topiko/bBot/Arduino/serial_due_rpi.ino

/*
  Serial Event example

  When new serial data arrives, this sketch adds it to a String.
  When a newline is received, the loop prints the string and clears it.

  A good test for this is to try it with a GPS receiver that sends out
  NMEA 0183 sentences.

  NOTE: The serialEvent() feature is not available on the Leonardo, Micro, or
  other ATmega32U4 based boards.

  created 9 May 2011
  by Tom Igoe

  This example code is in the public domain.

  http://www.arduino.cc/en/Tutorial/SerialEvent
*/

int inInt = 0;
int command[3] = {0, 0, 0};
int countSer = 0;
boolean report = false;  // whether the string is complete

void setup() {
  // initialize serial:
  Serial3.begin(115200);
}

void loop() {
  // print the int when newInt
  if (countSer == 1) {
    inInt += 1;
    commnad[0] = inInt;
  }
  else if (countSer == 2) {
    inInt += 2;
    commnad[1] = inInt;
  }
  else if (countSer == 3) {
    inInt += 3;
    commnad[2] = inInt;
    counter = 0;
    Serial3.print(command[0]);
    Serial3.print(command[1]);
    Serial3.print(command[2]);
  }
}

/*
  SerialEvent occurs whenever a new data comes in the hardware serial RX. This
  routine is run between each time loop() runs, so using delay inside loop can
  delay response. Multiple bytes of data may be available.
*/
void serialEvent3() {
  inInt = (int)Serial3.read();
  countSer += 1;
  //report = true;
  
  /*
  while (Serial3.available()) {
    // get the new byte:
    char inChar = (char)Serial3.read();
    
    // add it to the inputString:
    inputString += inChar;
    // if the incoming character is a newline, set a flag so the main loop can
    // do something about it:
    if (inChar == '\n') {
      stringComplete = true;
    }
  }
  */
}
