topiko/bBot/Raspberry/score.py

"""
MOdule to handle the performance scoring of Patric.
"""

from scipy.integrate import trapz
import numpy as np

def score_run(run_array):
    """
    Obtain a performance score given from run array.
    """
    if run_array is None:
        return np.inf

    times = run_array['times']
    thetas = run_array['theta']
    target_thetas = run_array['target_theta']
    run_l = run_array['run_l']
    target_l = run_array['target_l']


    tot_time = times[-1] - times[0]
    score = 0
    for vals, target_vals, mlt in [(thetas, target_thetas, 1),
                                   (run_l, target_l, 100)]:
        squared_diff = (vals - target_vals)**2*mlt**2
        score += trapz(squared_diff, times)/tot_time

    return score
    #(squared_diff[1:]*np.diff(times)).sum()/(times[-1] - times[0])
    #return trapz(squared_diff, times)/(times[-1] - times[0])
