topiko/bBot/Raspberry/simulate.py

"""
This is patrics simulation module.

Intention is so that one can run the balance cyckle as normal
and here we do simulations required.
"""

import numpy as np
from scipy.integrate import solve_ivp
from params import UPRIGHT_THETA, ALPHA, \
        GRAVITY_ACCEL, SIGMA_THETA,\
        SIMUL_LOOP_TIME, ALPHA_SIMUL, \
        INIT_THETA_DEV
import matplotlib.pyplot as plt
from modelpatric import get_thetadotdot
from score import score_run
from plot_run import plot_dynamics

class simulate_patric():

    def __init__(self, theta=UPRIGHT_THETA, thetadot=0, dt=.01):
        """
        Init.
        """
        self.theta = theta + INIT_THETA_DEV
        self.thetadot = thetadot
        self.time = 0
        self.dt = dt
        self.noise = True #False #True #False
        self.theta_noisy = self.theta
        #self.record_theta = np.zeros((int(SIMUL_LOOP_TIME//self.dt)+3, 4))
        self.idx = 0

    def reset_idx(self):
        self.idx = 0

    def run(self, state_dict, cmd_dict):
        """
        Propagate the dynamics by amount dt
        """
        accel = cmd_dict['a']
        def theta_derivs(t, theta_vec):
            theta = theta_vec[0]
            thetadot = theta_vec[1]

            thetadotdot = get_thetadotdot(theta, accel, alpha=ALPHA_SIMUL)
            return thetadot, thetadotdot

        sol = solve_ivp(theta_derivs,
                        [0, self.dt],
                        np.array([self.theta, self.thetadot]))

        thetas = sol['y'][0]
        thetadots = sol['y'][1]

        # Theta noise:
        theta_noise = np.random.normal(0, scale=SIGMA_THETA) if self.noise else 0
        self.theta = thetas[-1]
        self.theta_noisy = self.theta + theta_noise
        self.thetadot = thetadots[-1]
        self.time += self.dt


def display_simulation(ser, balance_loop):
    """
    This is the main loop plotting the simulation results.
    """
    i = 0
    cmd_dict = None
    state_dict = None
    kl = None
    while True:
        run_array, ser, status, cmd_dict, state_dict, kl \
                = balance_loop(ser,
                               run_time_max=SIMUL_LOOP_TIME, #*(i+1),
                               cmd_dict=cmd_dict,
                               state_dict=state_dict,
                               kl=kl)
        ser.reset_idx()

        print('SCORE:')
        print(score_run(run_array))

        plot_dynamics(run_array) #, ser.record_theta[:ser.idx])

        if status == 'fell':
            break
        i += 1


    return
